Bastelschlumpf/SnorkTracker/images/origin/HousingBlack.png

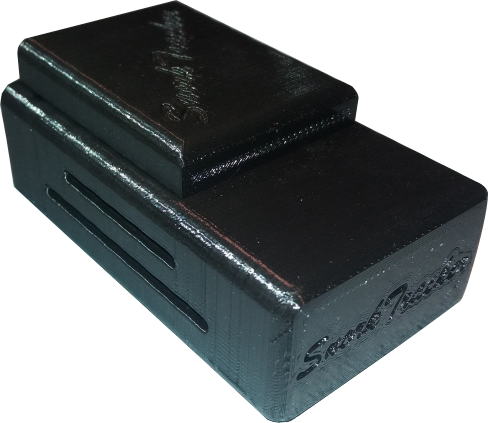
images/origin/HousingBlack.png
