Bastelschlumpf/SnorkTracker/tracker/Voltage.h

/*
   Copyright (C) 2018 SFini

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
   You should have received a copy of the GNU General Public License
   along with this program.  If not, see <http://www.gnu.org/licenses/>.
*/
/**
  * @file Voltage.h
  *
  * Class to read the power supply voltage.
  */

#define ANALOG_FACTOR 0.03 //!< Factor to the analog voltage divider

/**
  * Voltage Reader. Works with the voltage divider resistors and the analog input reader.
  */
class MyVoltage
{
protected:
   MyOptions &myOptions;        //!< Reference to global options
   MyData    &myData;           //!< Reference to global data

   long       lowPowerStartSec; //!< Switch off timestamp

public:
   MyVoltage(MyOptions &options, MyData &data);

   bool begin();

   void readVoltage();
};

/* ******************************************** */

/** Constructor */
MyVoltage::MyVoltage(MyOptions &options, MyData &data)
   : myOptions(options)
   , myData(data)
   , lowPowerStartSec(0)
{
}

/** Reads the voltage at startup. */
bool MyVoltage::begin()
{
   MyDbg(F("MyVoltage::begin"));
   pinMode(A0, INPUT);
   myData.voltage    = ANALOG_FACTOR * analogRead(A0); // Volt
   myData.isLowPower = myData.voltage < myOptions.powerSaveModeVoltage;
   lowPowerStartSec  = millis() / 1000;
}

/** Reads the power supply voltage and save the value in the data class. 
  * Add the lowPower time to the lowPowerActive and lowPowerPowerOn time. 
  */
void MyVoltage::readVoltage()
{
   bool isLowPower = false;
   long currSec    = millis() / 1000;
   
   myData.voltage = ANALOG_FACTOR * analogRead(A0); // Volt
   isLowPower     = myData.voltage < myOptions.powerSaveModeVoltage;

   if (myData.isLowPower && !isLowPower) { // Change to high power
      long lowPowerSec = currSec - lowPowerStartSec;

      myData.rtcData.lowPowerActiveTimeSec += lowPowerSec;
      if (myData.isPowerOn) {
         myData.rtcData.lowPowerPowerOnTimeSec += lowPowerSec;
      }
      MyDbg((String) F("Change to high power (V): ") + String(myData.voltage, 2));
   }
   if (!myData.isLowPower && isLowPower) { // Change to low power
      lowPowerStartSec = currSec;
      MyDbg((String) F("Change to low power (V): ") + String(myData.voltage, 2));
   }
   myData.isLowPower = isLowPower;
}
